xlh001/PLFM_RADAR/9_Firmware/9_2_FPGA/matched_filter_processing_chain.v

`timescale 1ns / 1ps

/**
 * matched_filter_processing_chain.v
 *
 * Pulse compression processing chain for AERIS-10 FMCW radar.
 * Implements: FFT(signal) → FFT(reference) → Conjugate multiply → IFFT
 *
 * This is a SIMULATION-COMPATIBLE implementation that replaces the Xilinx
 * FFT IP cores (FFT_enhanced) with behavioral Radix-2 DIT FFT engines.
 * For synthesis, replace the behavioral FFT instances with the actual
 * Xilinx xfft IP blocks.
 *
 * Interface contract (from matched_filter_multi_segment.v line 361):
 *   .clk, .reset_n
 *   .adc_data_i, .adc_data_q, .adc_valid      <- from input buffer
 *   .chirp_counter                              <- 6-bit frame counter
 *   .long_chirp_real/imag, .short_chirp_real/imag <- reference (time-domain)
 *   .range_profile_i, .range_profile_q, .range_profile_valid -> output
 *   .chain_state                                -> 4-bit status
 *
 * Clock domain: clk (100 MHz system clock)
 * Data format:  16-bit signed (Q15 fixed-point)
 * FFT size:     1024 points
 *
 * Pipeline states:
 *   IDLE -> FWD_FFT (collect 1024 samples + bit-reverse copy)
 *        -> FWD_BUTTERFLY (forward FFT of signal)
 *        -> REF_BITREV (bit-reverse copy reference into work arrays)
 *        -> REF_BUTTERFLY (forward FFT of reference)
 *        -> MULTIPLY (conjugate multiply in freq domain)
 *        -> INV_BITREV (bit-reverse copy product)
 *        -> INV_BUTTERFLY (inverse FFT + 1/N scaling)
 *        -> OUTPUT (stream 1024 samples)
 *        -> DONE -> IDLE
 */

module matched_filter_processing_chain (
    input wire clk,
    input wire reset_n,

    // Input ADC data (from matched_filter_multi_segment buffer)
    input wire [15:0] adc_data_i,
    input wire [15:0] adc_data_q,
    input wire adc_valid,

    // Chirp counter (for future multi-chirp modes)
    input wire [5:0] chirp_counter,

    // Reference chirp (time-domain, latency-aligned by upstream buffer)
    input wire [15:0] long_chirp_real,
    input wire [15:0] long_chirp_imag,
    input wire [15:0] short_chirp_real,
    input wire [15:0] short_chirp_imag,

    // Output: range profile (pulse-compressed)
    output wire signed [15:0] range_profile_i,
    output wire signed [15:0] range_profile_q,
    output wire range_profile_valid,

    // Status
    output wire [3:0] chain_state
);

// ============================================================================
// PARAMETERS
// ============================================================================
localparam FFT_SIZE   = 1024;
localparam ADDR_BITS  = 10;    // log2(1024)

// State encoding (4-bit, up to 16 states)
localparam [3:0] ST_IDLE           = 4'd0;
localparam [3:0] ST_FWD_FFT        = 4'd1;   // Collect samples + bit-reverse
localparam [3:0] ST_FWD_BUTTERFLY  = 4'd2;   // Signal FFT butterflies
localparam [3:0] ST_REF_BITREV     = 4'd3;   // Bit-reverse copy reference
localparam [3:0] ST_REF_BUTTERFLY  = 4'd4;   // Reference FFT butterflies
localparam [3:0] ST_MULTIPLY       = 4'd5;   // Conjugate multiply
localparam [3:0] ST_INV_BITREV     = 4'd6;   // Bit-reverse copy product
localparam [3:0] ST_INV_BUTTERFLY  = 4'd7;   // IFFT butterflies + scale
localparam [3:0] ST_OUTPUT         = 4'd8;   // Stream results
localparam [3:0] ST_DONE           = 4'd9;   // Return to idle

reg [3:0] state;

// ============================================================================
// SIGNAL BUFFERS
// ============================================================================
// Input sample counter
reg [ADDR_BITS:0] fwd_in_count;     // 0..1024
reg fwd_frame_done;                  // All 1024 samples received

// Signal time-domain buffer
reg signed [15:0] fwd_buf_i [0:FFT_SIZE-1];
reg signed [15:0] fwd_buf_q [0:FFT_SIZE-1];

// Signal FFT output (frequency domain)
reg signed [15:0] fwd_out_i [0:FFT_SIZE-1];
reg signed [15:0] fwd_out_q [0:FFT_SIZE-1];
reg fwd_out_valid;
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
